feichtinger/class-D-amp/Fotos/Verst-1.jpg

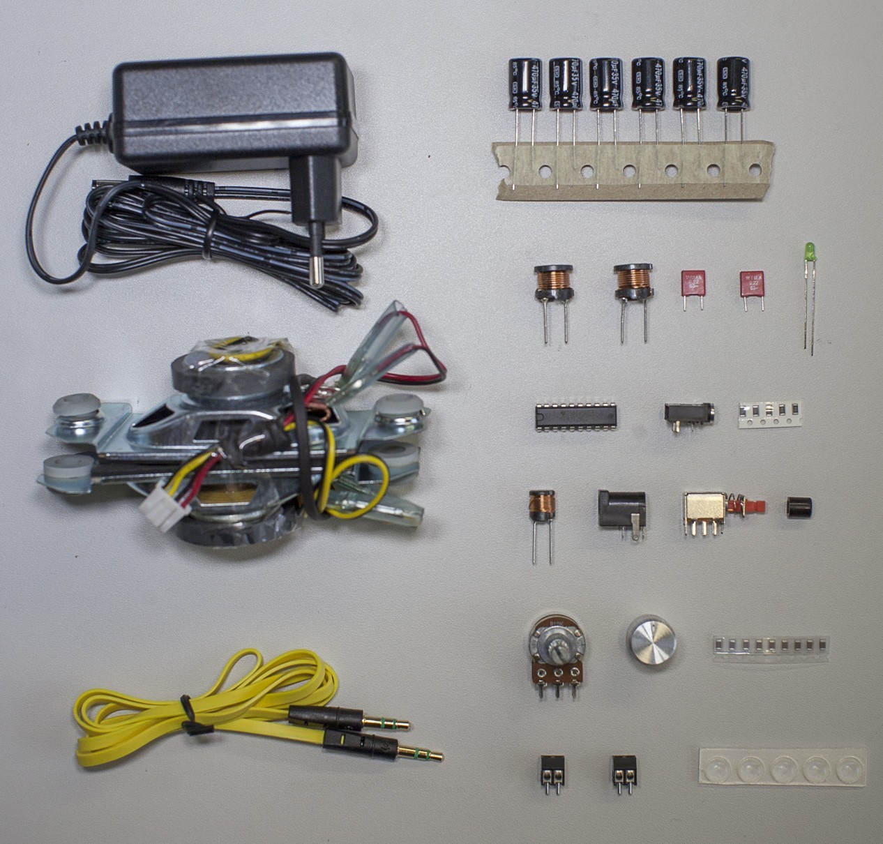
Fotos/Verst-1.jpg
