feichtinger/class-D-amp/Fotos/Verst-2.jpg

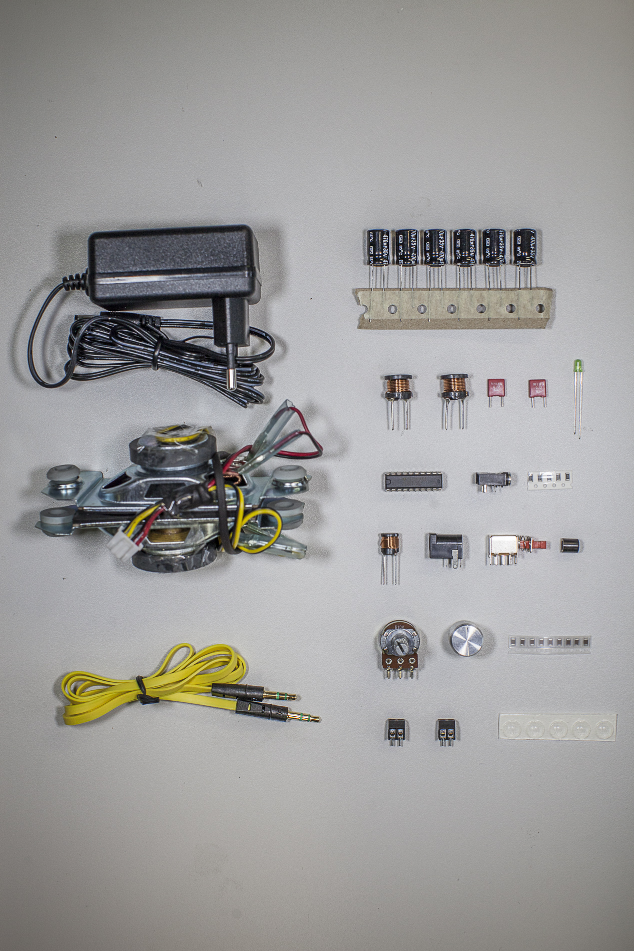
Fotos/Verst-2.jpg
