feichtinger/class-D-amp/Fotos/Verst-5.jpg

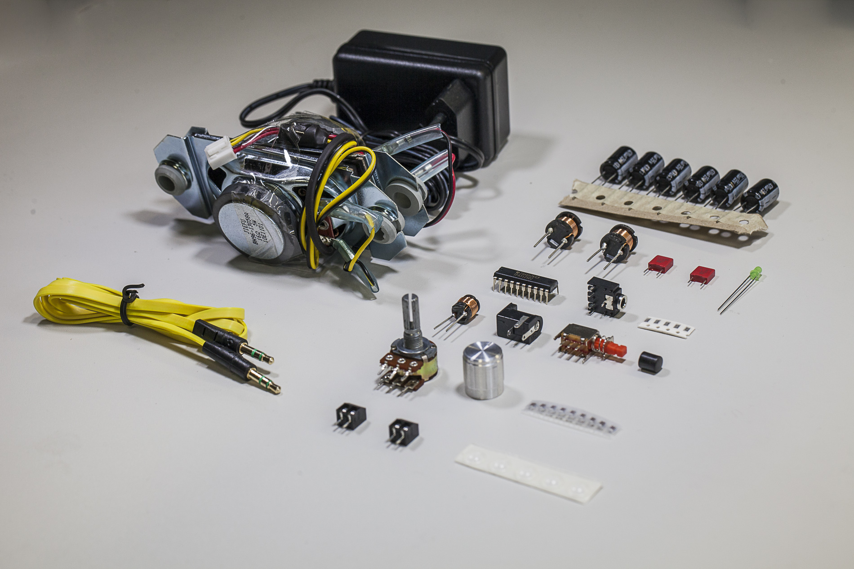
Fotos/Verst-5.jpg
