feichtinger/class-D-amp/Simulationen/test_filter.asc

C1: cap; 2.25045e-07
C2: cap; 3.07487e-07
C3: cap; 8.23786e-08
L1: ind; 0.000205946
L2: ind; 0.000768718
L3: ind; 0.000562613
R1: res; 50
R2: res; 50
V1: voltage; ""; AC 1
Named nets: 0, OUT
.ac dec 100 20 100k
Tiefpassfilter
Ausgang
