feichtinger/class-D-amp/Simulationen/class_D_principe.asc

A1: diffschmtbuf; Vhigh=1, Vlow=-1, Vt=0, Vh=0, Rout=1m
C4: cap; 2.25045e-07
L4: ind; 0.000562613
R2: res; 50
R3: res; 50
V1: voltage; PULSE(-1 1 0 {1/(2*f_PWM)} {1/(2*f_PWM)} 0 {1.0/f_PWM})
V2: voltage; SINE(0 0.3 440)
V5: voltage; SINE(0 1 220)
Named nets: 0, TRI, IN, DIG, OUT
.tran 0 2m 100u 10n uic
.param f_PWM=300k
Dreieckgenerator
Eingangssignal
Komparator
Ausgang
Tiefpassfilter
