feichtinger/class-D-amp/Simulationen/output_filter.asc

C1: cap; 220n
L1: ind; 33µ
R1: res; 16
R2: res; 82m
V1: voltage; ""; AC 1
Named nets: 0, OUT
.ac dec 1000 20 1Meg
