feichtinger/class-D-amp/Simulationen/supply_filter.asc

C1: cap; 1.88m
C2: cap; 1.88m
I1: current; ""; AC 1
L1: ind; 330µ
L2: ind; 330µ
R1: res; 16
R2: res; 0.7
R4: res; 0.7
V1: voltage; ""; AC 1
Named nets: 0, OUT_NOISE, OUT_LOAD
.ac dec 1000 20 20000
output voltage related to supply ripple
output voltage related to load current (source impedance)
